jiangjin1996/capstone-pcb/pcb/footprint_3d/T495D106K035ATE300.stp

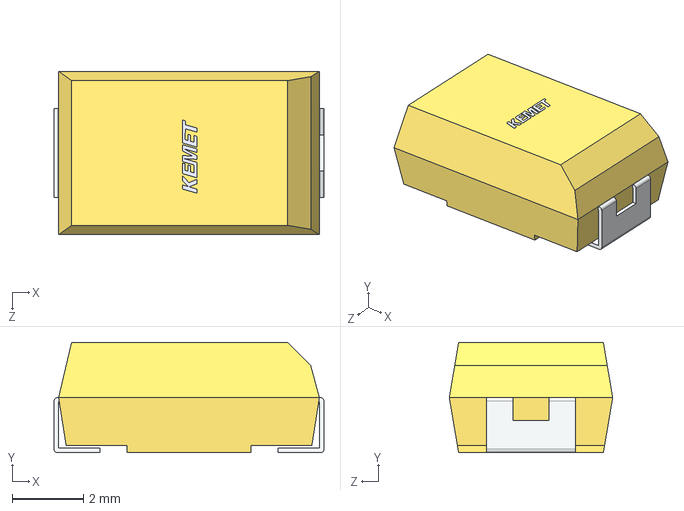
[picture p15: CAD file, 2026-02-16]
pcb/footprint_3d/T495D106K035ATE300.stp
7.60 x 3.11 x 4.60 mm
