jiangjin1996/capstone-pcb/pcb/footprint_3d/ECS-80-18-5PX-GM-TR.stp

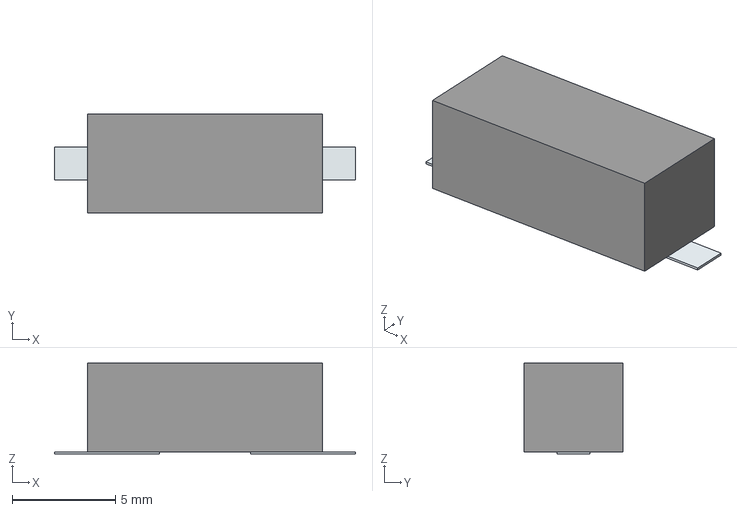
[picture p16: CAD file, 2026-02-16]
pcb/footprint_3d/ECS-80-18-5PX-GM-TR.stp
14.6 x 4.80 x 4.40 mm
Pins
