jiangjin1996/capstone-pcb/pcb/footprint_3d/ESQ-126-39-G-D.stp

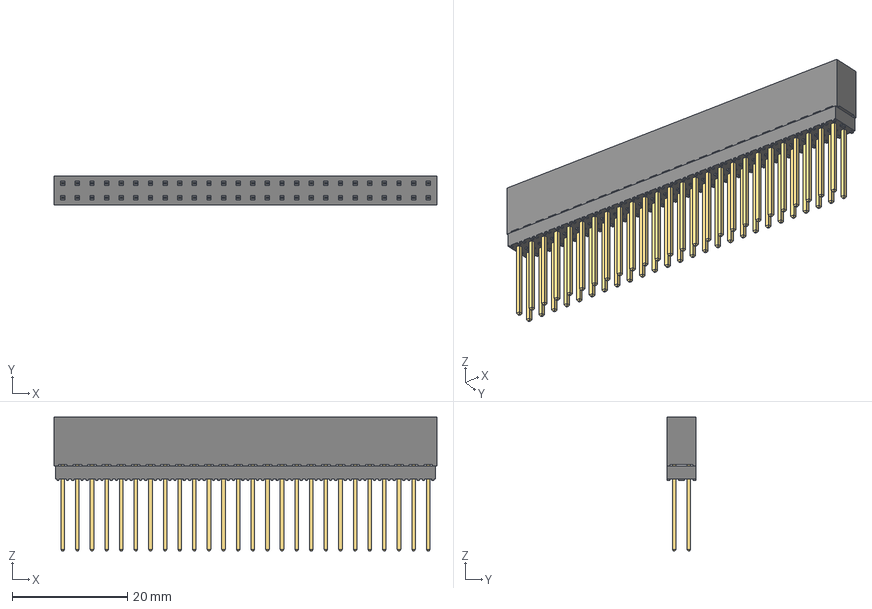
[picture p17: CAD file, 2026-02-15]
pcb/footprint_3d/ESQ-126-39-G-D.stp
66.5 x 5.08 x 23.2 mm
ESQ-126-39-G-D_pins
ESQ-126-39-G-D2_pins
ESQ-126-39-G-D-LL_bpins
ESQ-126-39-G-D_socket
