jiangjin1996/capstone-pcb/pcb/footprint_3d/LMT87DCKT.step

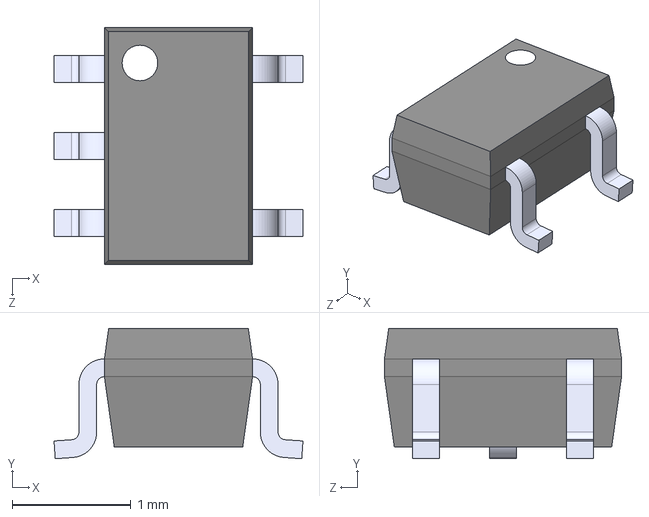
[picture p18: CAD file, 2026-02-15]
pcb/footprint_3d/LMT87DCKT.step
2.10 x 1.10 x 2.00 mm
