jiangjin1996/capstone-pcb/pcb/footprint_3d/C0805C224M5VACTU.step

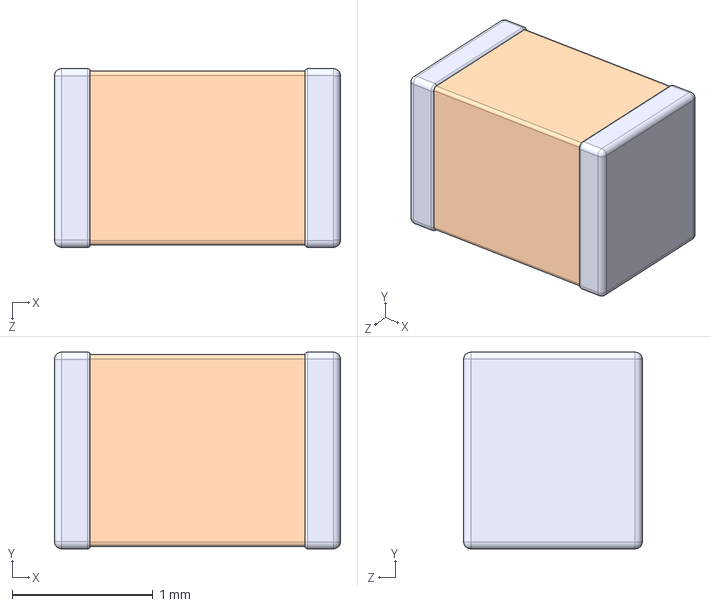
[picture p19: CAD file, 2026-02-15]
pcb/footprint_3d/C0805C224M5VACTU.step
2.03 x 1.40 x 1.27 mm
