jiangjin1996/capstone-pcb/pcb/footprint_3d/CL32A157MQVNNNE.STEP

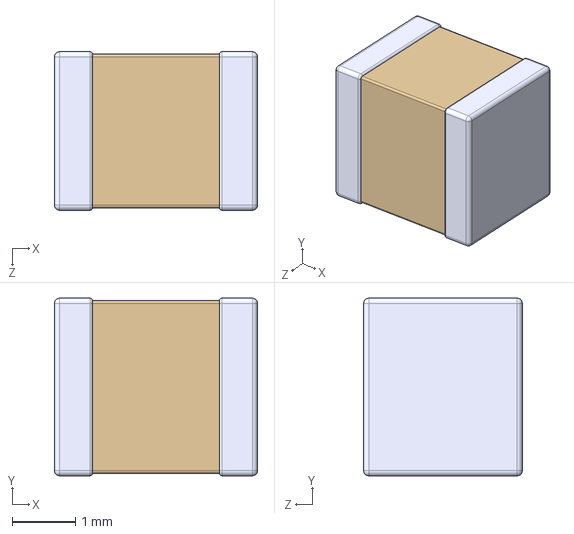
[picture p20: CAD file, 2026-02-15]
pcb/footprint_3d/CL32A157MQVNNNE.STEP
3.20 x 2.80 x 2.50 mm
