jiangjin1996/capstone-pcb/pcb/footprint_3d/MS168-10S.step

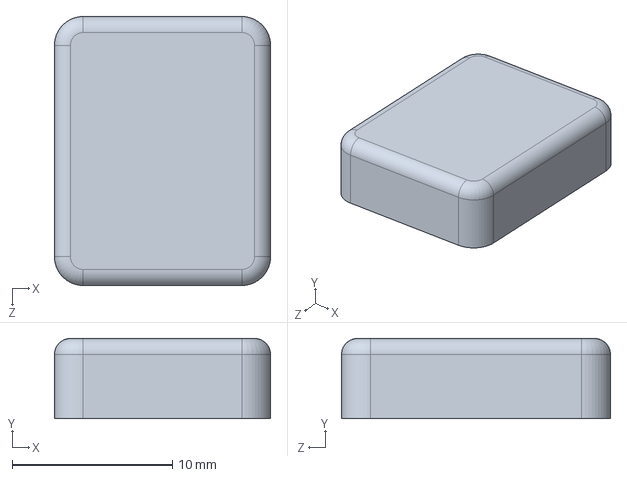
[picture p21: CAD file, 2025-12-14]
pcb/footprint_3d/MS168-10S.step
13.5 x 5.00 x 16.8 mm
