jiangjin1996/capstone-pcb/pcb/footprint_3d/MS110-20S.step

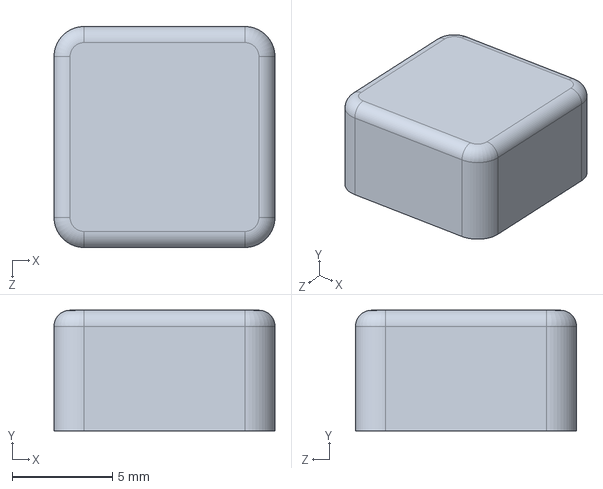
[picture p22: CAD file, 2025-12-14]
pcb/footprint_3d/MS110-20S.step
11.0 x 6.00 x 11.0 mm
