jiangjin1996/capstone-pcb/pcb/footprint_3d/AD844JRZ_16_REEL7.step

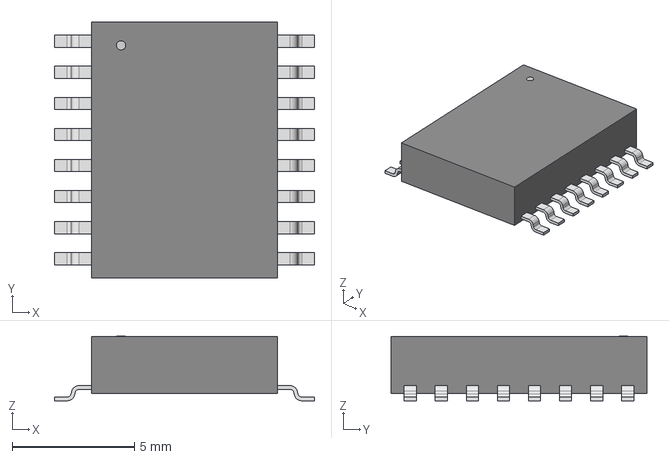
[picture p23: CAD file, 2025-12-14]
pcb/footprint_3d/AD844JRZ_16_REEL7.step
10.6 x 10.5 x 2.64 mm
