jiangjin1996/capstone-pcb/pcb/footprint_3d/MS182-10C-NS.step

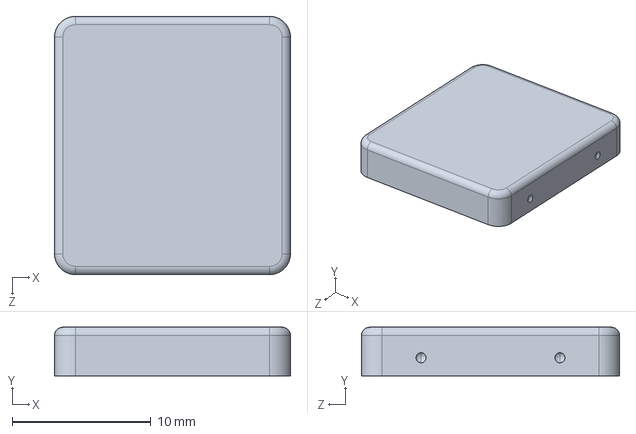
[picture p24: CAD file, 2025-12-14]
pcb/footprint_3d/MS182-10C-NS.step
17.0 x 3.50 x 18.6 mm
