jiangjin1996/capstone-pcb/pcb/footprint_3d/REF192GSZ_REEL7.step

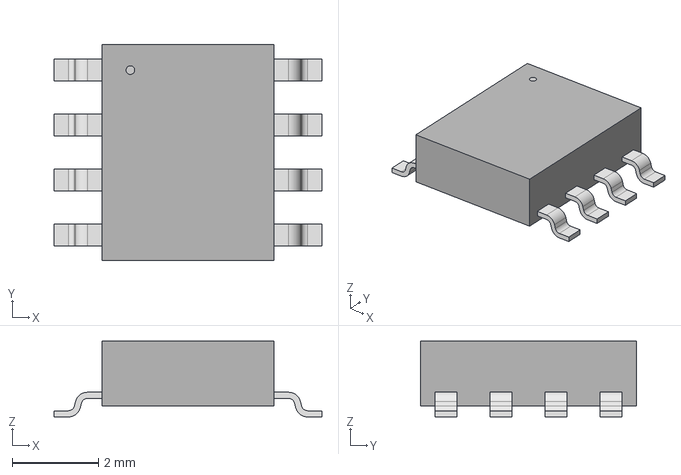
[picture p25: CAD file, 2025-12-14]
pcb/footprint_3d/REF192GSZ_REEL7.step
6.20 x 5.00 x 1.75 mm
