jiangjin1996/capstone-pcb/pcb/footprint_3d/LTC4300A-1IMS8_PBF.step

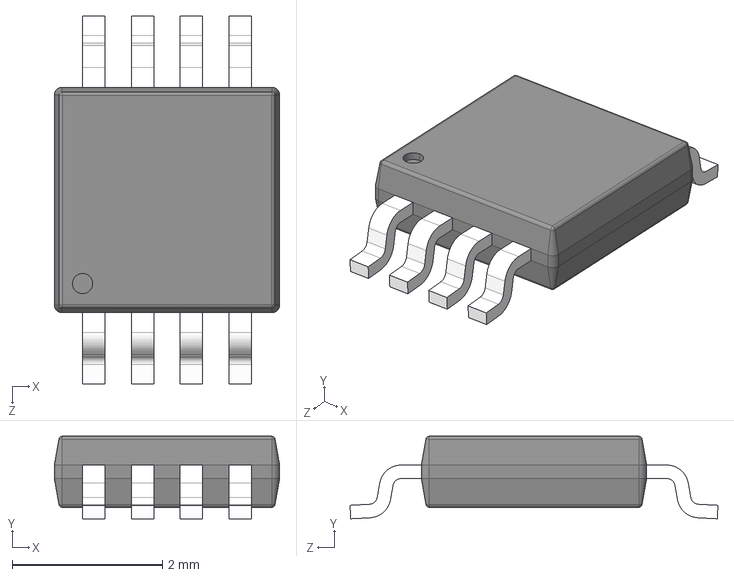
[picture p26: CAD file, 2025-12-14]
pcb/footprint_3d/LTC4300A-1IMS8_PBF.step
3.00 x 1.10 x 4.90 mm
