jiangjin1996/capstone-pcb/pcb/footprint_3d/TPS2069CDBVR.step

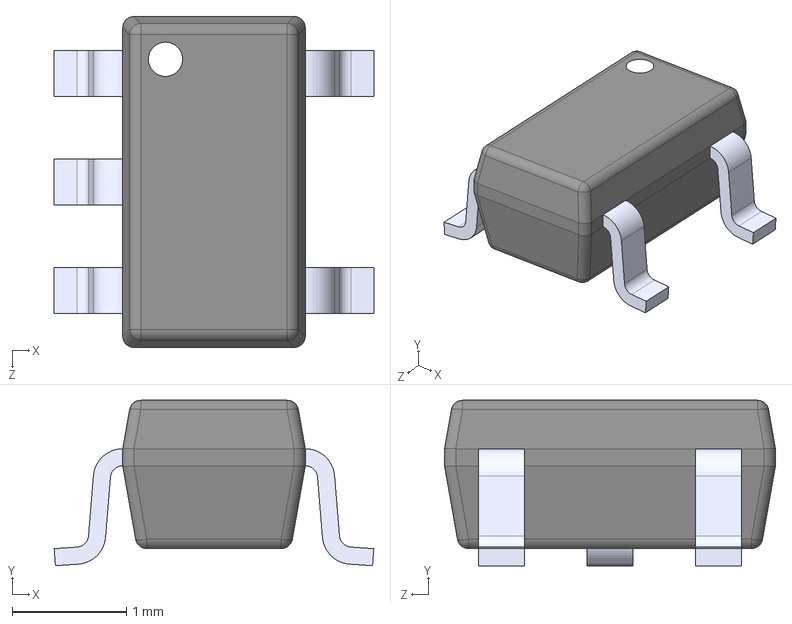
[picture p27: CAD file, 2025-12-14]
pcb/footprint_3d/TPS2069CDBVR.step
2.80 x 1.45 x 2.90 mm
