jiangjin1996/capstone-pcb/pcb/footprint_3d/LM35DM.stp

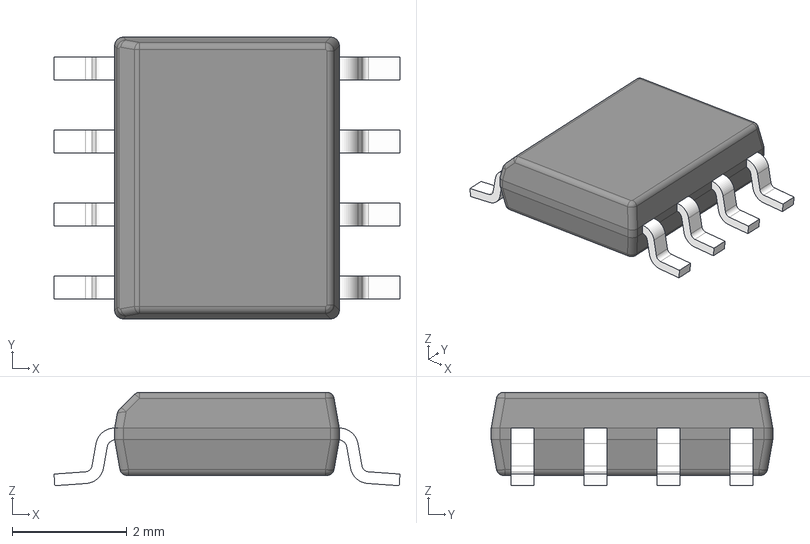
[picture p28: CAD file, 2025-02-11]
pcb/footprint_3d/LM35DM.stp
6.02 x 4.90 x 1.63 mm
BODY-SO
LEAD-D0008A x 8
